smartboxchannel/EFEKTA-Pool-Temperature-Sensor/IMAGES/IMG20230716155857.jpg

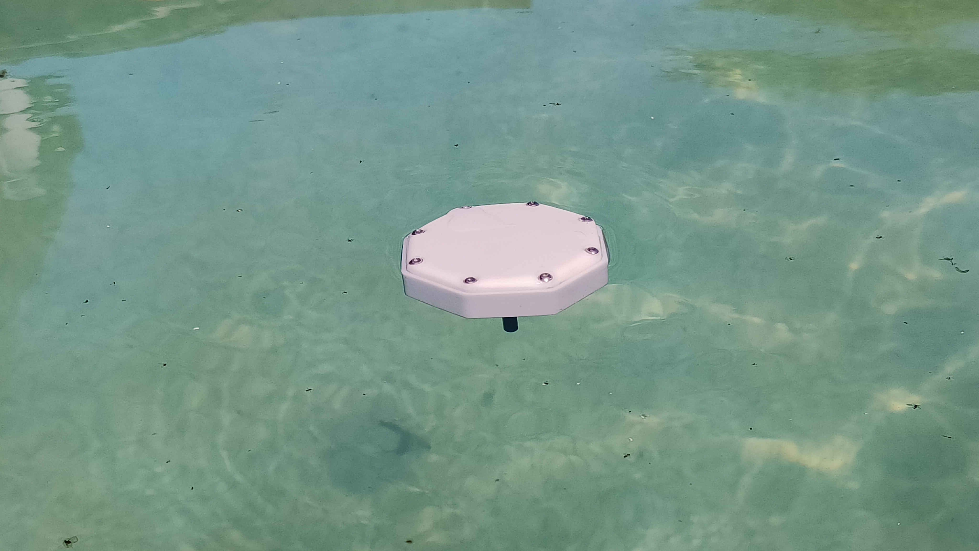
IMAGES/IMG20230716155857.jpg
