smartboxchannel/EFEKTA-Pool-Temperature-Sensor/IMAGES/IMG20230808213855.jpg

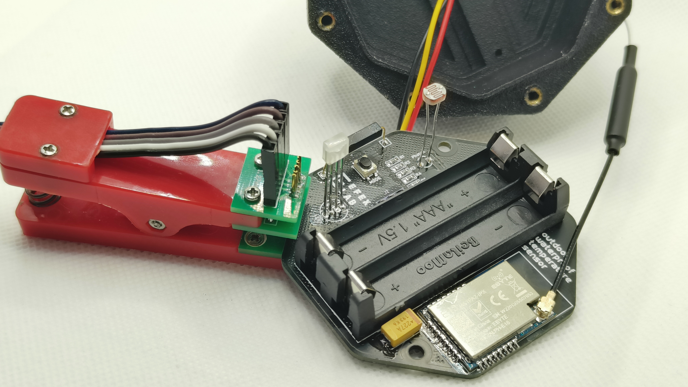
IMAGES/IMG20230808213855.jpg
