smartboxchannel/EFEKTA-Pool-Temperature-Sensor/IMAGES/IMG_20230716_162220_0334.jpg

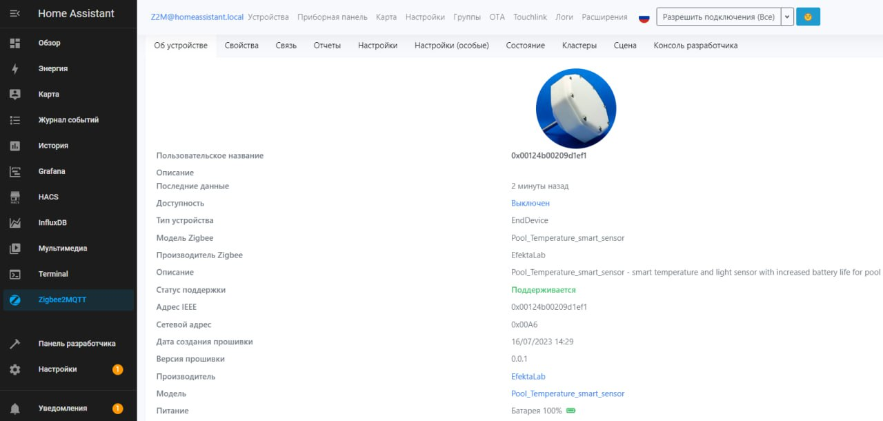
IMAGES/IMG_20230716_162220_0334.jpg
