smartboxchannel/EFEKTA-Pool-Temperature-Sensor/IMAGES/IMG_20230716_162222_0828.jpg

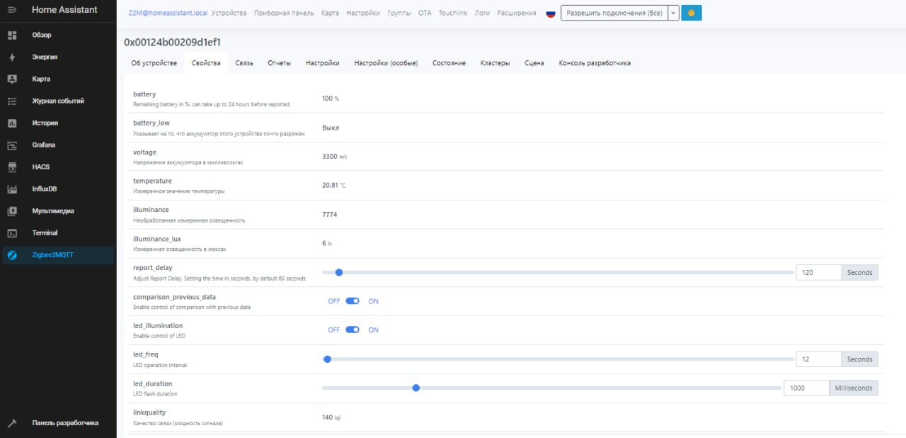
IMAGES/IMG_20230716_162222_0828.jpg
