smartboxchannel/EFEKTA-Pool-Temperature-Sensor/PROJECT SOURC/POOL_TEMP/zstack-lib/hal_key.c

/**************************************************************************************************
 *                                            INCLUDES
 **************************************************************************************************/
#include "hal_key.h"
#include "OnBoard.h"
#include "utils.h"

#include "hal_adc.h"
#include "hal_defs.h"
#include "hal_drivers.h"
#include "hal_led.h"
#include "hal_mcu.h"
#include "hal_types.h"
#include "osal.h"

/**************************************************************************************************
 *                                              MACROS
 **************************************************************************************************/

#ifndef HAL_KEY_P0_INPUT_PINS
  #define HAL_KEY_P0_INPUT_PINS 0x00
#endif

#ifndef HAL_KEY_P1_INPUT_PINS
  #define HAL_KEY_P1_INPUT_PINS 0x00
#endif

#ifndef HAL_KEY_P2_INPUT_PINS
  #define HAL_KEY_P2_INPUT_PINS 0x00
#endif


#ifndef HAL_KEY_P0_INPUT_PINS_EDGE
  #define HAL_KEY_P0_INPUT_PINS_EDGE HAL_KEY_FALLING_EDGE
#endif

#ifndef HAL_KEY_P1_INPUT_PINS_EDGE
  #define HAL_KEY_P1_INPUT_PINS_EDGE HAL_KEY_FALLING_EDGE
#endif

#ifndef HAL_KEY_P2_INPUT_PINS_EDGE
  #define HAL_KEY_P2_INPUT_PINS_EDGE HAL_KEY_FALLING_EDGE
#endif
/**************************************************************************************************
 *                                            CONSTANTS
 **************************************************************************************************/

uint8 portNum = 0;
uint8 pinNum = 0;

#define HAL_KEY_DEBOUNCE_VALUE 25

#define HAL_KEY_P0_EDGE_BITS HAL_KEY_BIT0
#define HAL_KEY_P1_EDGE_BITS (HAL_KEY_BIT1 | HAL_KEY_BIT2)
#define HAL_KEY_P2_EDGE_BITS HAL_KEY_BIT3

/**************************************************************************************************
 *                                            TYPEDEFS
 **************************************************************************************************/

/**************************************************************************************************
 *                                        GLOBAL VARIABLES
 **************************************************************************************************/
bool Hal_KeyIntEnable;
/**************************************************************************************************
 *                                        FUNCTIONS - Local
 **************************************************************************************************/
void halProcessKeyInterrupt(uint8 portNum);

void HalKeyPoll(void) {
    uint8 pinStatus = 0;
    bool isPressed = false;
    switch (portNum) {
    case HAL_KEY_PORT0:
        PICTL ^= HAL_KEY_P0_EDGE_BITS; // flip edge bit
        pinStatus = P0 & pinNum;
        isPressed = HAL_KEY_P0_INPUT_PINS_EDGE != !!(pinStatus);
        break;

    case HAL_KEY_PORT1:
        PICTL ^= HAL_KEY_P1_EDGE_BITS; // flip edge bit
        pinStatus = P1 & pinNum;
        isPressed = HAL_KEY_P1_INPUT_PINS_EDGE != !!(pinStatus);
        break;

    case HAL_KEY_PORT2:
        PICTL ^= HAL_KEY_P2_EDGE_BITS; // flip edge bit
        pinStatus = P2 & pinNum;
        isPressed = HAL_KEY_P2_INPUT_PINS_EDGE != !!(pinStatus);
        break;

    default:
        break;
    }
    OnBoard_SendKeys(pinNum, (isPressed ? HAL_KEY_PRESS : HAL_KEY_RELEASE) | portNum);
}

void HalKeyInit(void) {
#if HAL_KEY_P0_INPUT_PINS
    P0SEL &= ~HAL_KEY_P0_INPUT_PINS;
    P0DIR &= ~(HAL_KEY_P0_INPUT_PINS);
#endif

#if HAL_KEY_P1_INPUT_PINS
    P1SEL &= ~HAL_KEY_P1_INPUT_PINS;
    P1DIR &= ~(HAL_KEY_P1_INPUT_PINS);
#endif

#if HAL_KEY_P2_INPUT_PINS
    P2SEL &= ~HAL_KEY_P2_INPUT_PINS;
    P2DIR &= ~(HAL_KEY_P2_INPUT_PINS);
#endif

}

void HalKeyConfig(bool interruptEnable, halKeyCBack_t cback) {
    Hal_KeyIntEnable = true;

#if HAL_KEY_P0_INPUT_PINS
    P0IEN |= HAL_KEY_P0_INPUT_PINS;
    IEN1 |= HAL_KEY_BIT5;            // enable port0 int
    P0INP &= ~HAL_KEY_P0_INPUT_PINS; // Pullup/pulldown
#if (HAL_KEY_P0_INPUT_PINS_EDGE == HAL_KEY_FALLING_EDGE)
    P2INP &= ~HAL_KEY_BIT5; // pull up
    MicroWait(50);
    PICTL |= HAL_KEY_P0_EDGE_BITS; // set falling edge on port
#else
    P2INP |= HAL_KEY_BIT5; // pull down
    MicroWait(50);
    PICTL &= ~(HAL_KEY_P0_EDGE_BITS);
#endif

#endif

#if HAL_KEY_P1_INPUT_PINS
    P1IEN |= HAL_KEY_P1_INPUT_PINS;
    IEN2 |= HAL_KEY_BIT4; // enable port1 int
    P1INP &= ~HAL_KEY_P1_INPUT_PINS; //Pullup/pulldown 
#if (HAL_KEY_P1_INPUT_PINS_EDGE == HAL_KEY_FALLING_EDGE)
    P2INP &= ~HAL_KEY_BIT6;        // pull up
    MicroWait(50);
    PICTL |= HAL_KEY_P1_EDGE_BITS; // set falling edge on port
#else
    P2INP |= HAL_KEY_BIT6; // pull down
    MicroWait(50);
    PICTL &= ~HAL_KEY_P1_EDGE_BITS;
#endif

#endif

#if HAL_KEY_P2_INPUT_PINS
    P2IEN |= HAL_KEY_P2_INPUT_PINS;
    IEN2 |= HAL_KEY_BIT1; // enable port2 int
    P2INP &= ~HAL_KEY_P2_INPUT_PINS; //Pullup/pulldown
#if (HAL_KEY_P2_INPUT_PINS_EDGE == HAL_KEY_FALLING_EDGE)
    P2INP &= ~HAL_KEY_BIT7;        // pull up
    MicroWait(50);
    PICTL |= HAL_KEY_P2_EDGE_BITS; // set falling edge on port
#else
    P2INP |= HAL_KEY_BIT7; // pull down
    MicroWait(50);
    PICTL &= ~HAL_KEY_P2_EDGE_BITS;
#endif

#endif
}

void halProcessKeyInterrupt(uint8 _portNum) {
    portNum = _portNum;
    switch (_portNum) {
    case HAL_KEY_PORT0:
        pinNum = P0IFG & HAL_KEY_P0_INPUT_PINS;
        break;

    case HAL_KEY_PORT1:
        pinNum = P1IFG & HAL_KEY_P1_INPUT_PINS;
        break;

    case HAL_KEY_PORT2:
        pinNum = P2IFG & HAL_KEY_P2_INPUT_PINS;
        break;
    default:
        break;
    }
    osal_start_timerEx(Hal_TaskID, HAL_KEY_EVENT, HAL_KEY_DEBOUNCE_VALUE);
}

void HalKeyEnterSleep(void) {
    uint8 clkcmd = CLKCONCMD;
    uint8 clksta = CLKCONSTA;
    // Switch to 16MHz before setting the DC/DC to bypass to reduce risk of flash corruption
    CLKCONCMD = (CLKCONCMD_16MHZ | OSC_32KHZ);
    // wait till clock speed stablizes
    while (CLKCONSTA != (CLKCONCMD_16MHZ | OSC_32KHZ))
        ;

    CLKCONCMD = clkcmd;
    while (CLKCONSTA != (clksta))
        ;
}

uint8 HalKeyExitSleep(void) {
    uint8 clkcmd = CLKCONCMD;
    // Switch to 16MHz before setting the DC/DC to on to reduce risk of flash corruption
    CLKCONCMD = (CLKCONCMD_16MHZ | OSC_32KHZ);
    // wait till clock speed stablizes
    while (CLKCONSTA != (CLKCONCMD_16MHZ | OSC_32KHZ))
        ;

    CLKCONCMD = clkcmd;

    // /* Wake up and read keys */
    return (HalKeyRead());
}

#if HAL_KEY_P0_INPUT_PINS
HAL_ISR_FUNCTION(halKeyPort0Isr, P0INT_VECTOR) {
    HAL_ENTER_ISR();

    if (P0IFG & HAL_KEY_P0_INPUT_PINS) {
        halProcessKeyInterrupt(HAL_KEY_PORT0);
    }

    P0IFG = 0; //&= ~HAL_KEY_P0_INPUT_PINS;
    P0IF = 0;

    CLEAR_SLEEP_MODE();
    HAL_EXIT_ISR();
}
#endif

#if HAL_KEY_P1_INPUT_PINS
HAL_ISR_FUNCTION(halKeyPort1Isr, P1INT_VECTOR) {
    HAL_ENTER_ISR();

    if (P1IFG & HAL_KEY_P1_INPUT_PINS) {
        halProcessKeyInterrupt(HAL_KEY_PORT1);
    }

    P1IFG = 0; //&= ~HAL_KEY_P1_INPUT_PINS;
    P1IF = 0;

    CLEAR_SLEEP_MODE();
    HAL_EXIT_ISR();
}
#endif

#if HAL_KEY_P2_INPUT_PINS
HAL_ISR_FUNCTION(halKeyPort2Isr, P2INT_VECTOR) {
    HAL_ENTER_ISR();

    if (P2IFG & HAL_KEY_P2_INPUT_PINS) {
        halProcessKeyInterrupt(HAL_KEY_PORT2);
    }

    P2IFG = 0; //&= ~HAL_KEY_P2_INPUT_PINS;
    P2IF = 0;

    CLEAR_SLEEP_MODE();
    HAL_EXIT_ISR();
}
#endif



uint8 HalKeyRead ( void ){
    return 0;
}
