smartboxchannel/EFEKTA-Pool-Temperature-Sensor/PROJECT SOURC/POOL_TEMP/zstack-lib/utils.c

#include "utils.h"
#include "hal_adc.h"

double mapRange(double a1, double a2, double b1, double b2, double s) {
    double result = b1 + (s - a1) * (b2 - b1) / (a2 - a1);
    return MIN(b2, MAX(result, b1));
}

uint16 adcReadSampled(uint8 channel, uint8 resolution, uint8 reference, uint8 samplesCount) {
    HalAdcSetReference(reference);
    uint32 samplesSum = 0;
    for (uint8 i = 0; i < samplesCount; i++) {
        samplesSum += HalAdcRead(channel, resolution);
    }
    return samplesSum /samplesCount;
}
